Amolpagare10/EE344_Electronic_Design_lab/3d_models/Box_CAD_Sketch.png

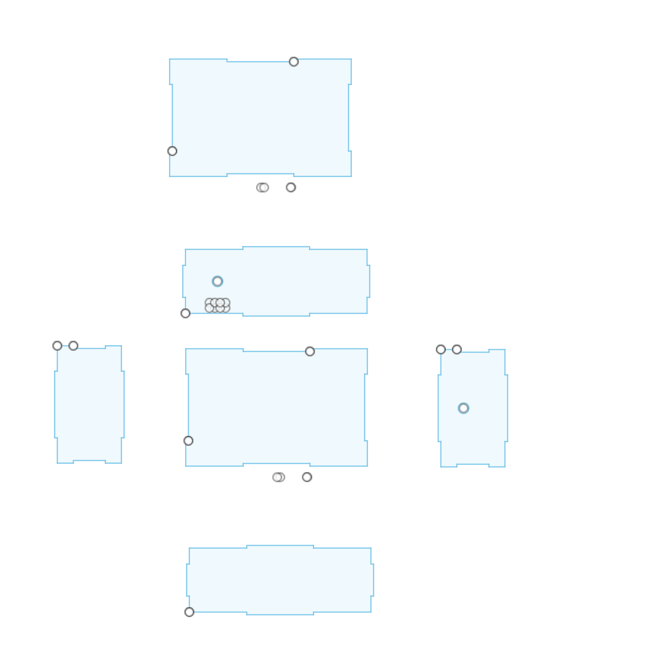
3d_models/Box_CAD_Sketch.png
