Amolpagare10/EE344_Electronic_Design_lab/images/7.jpg

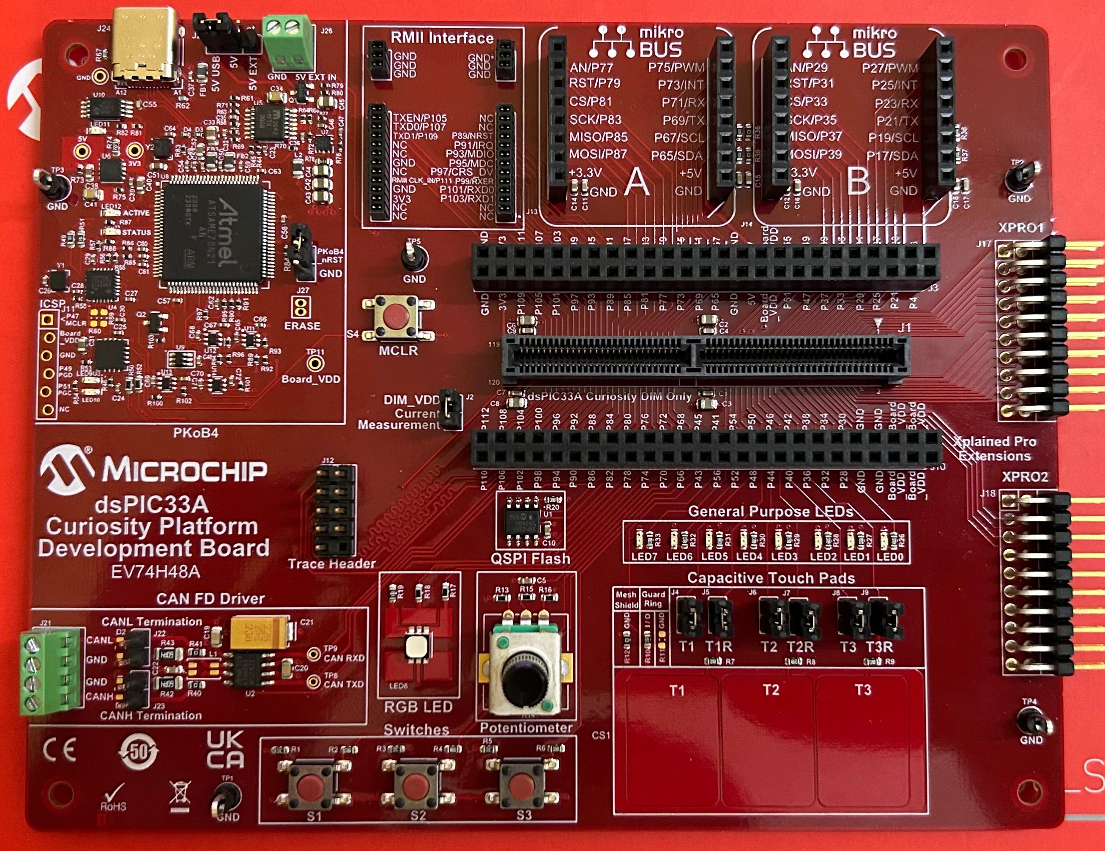
images/7.jpg
