Amolpagare10/EE344_Electronic_Design_lab/images/PCB_view.jpg

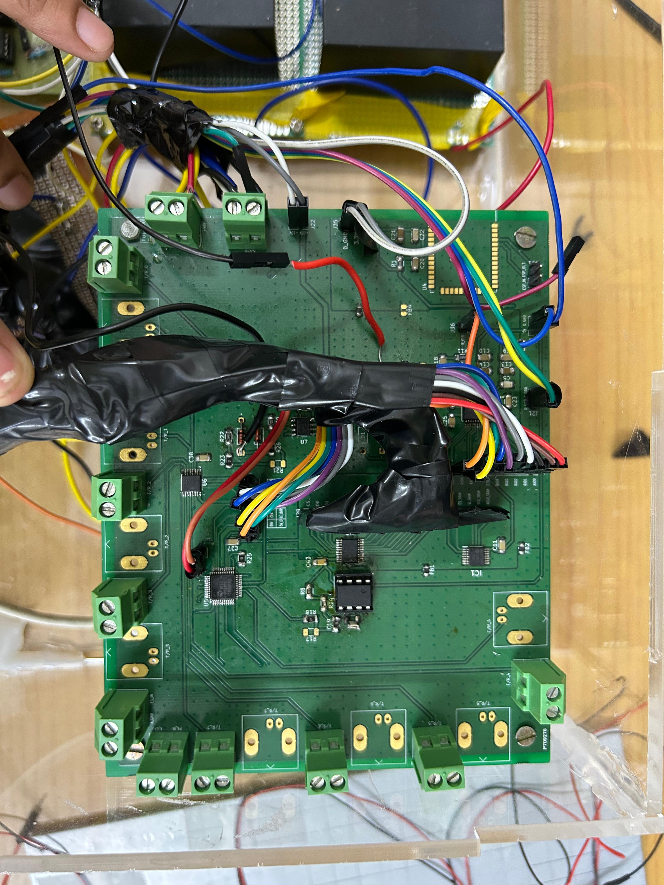
images/PCB_view.jpg
