Amolpagare10/EE344_Electronic_Design_lab/others/extras/ADC_test.jpg

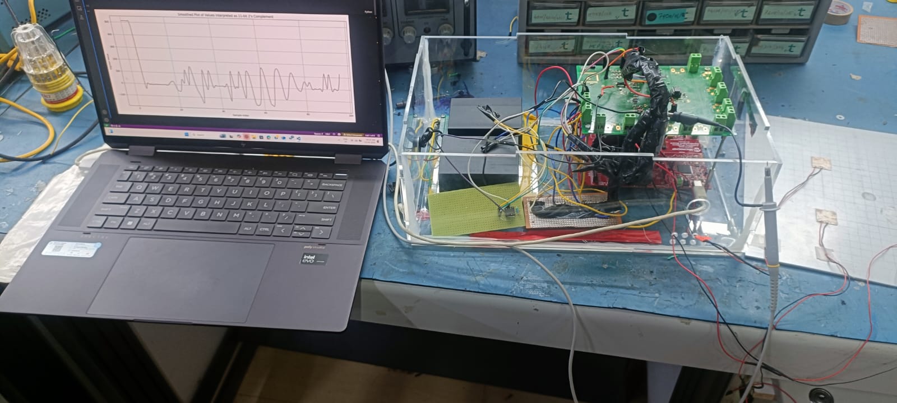
others/extras/ADC_test.jpg
